robertpetcu/inktime/Images/ecran.png

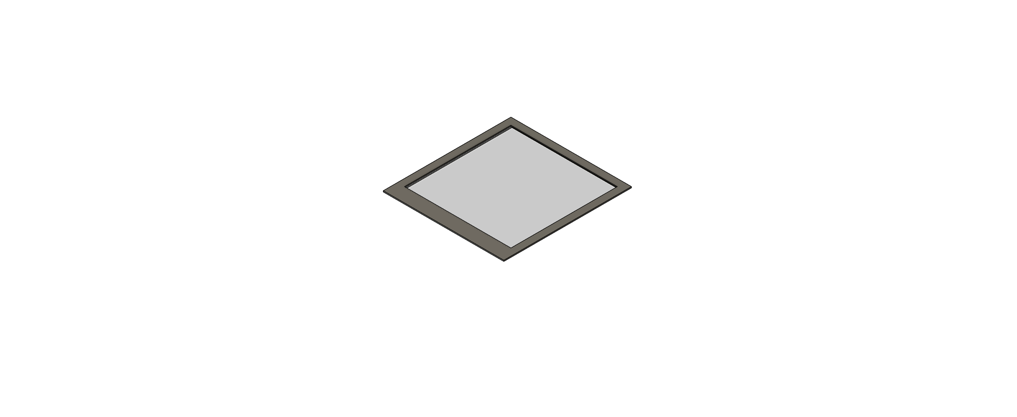
Images/ecran.png
