robertpetcu/inktime/Images/EXPLODED.png

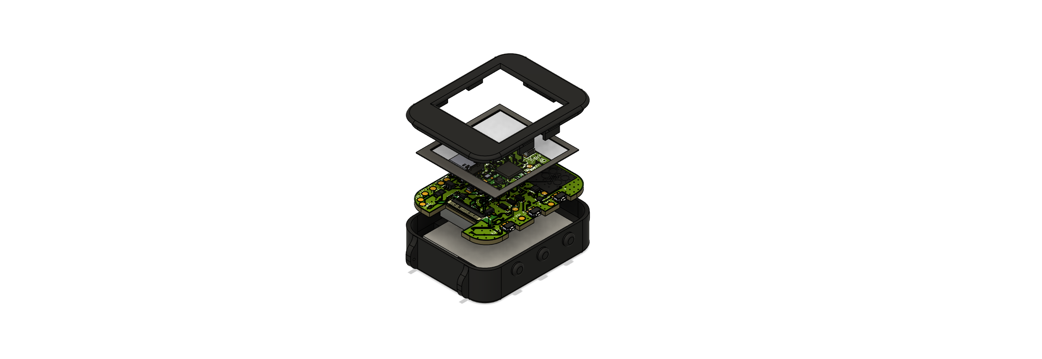
Images/EXPLODED.png
